janleroux/proj-roro/316941 (1).png

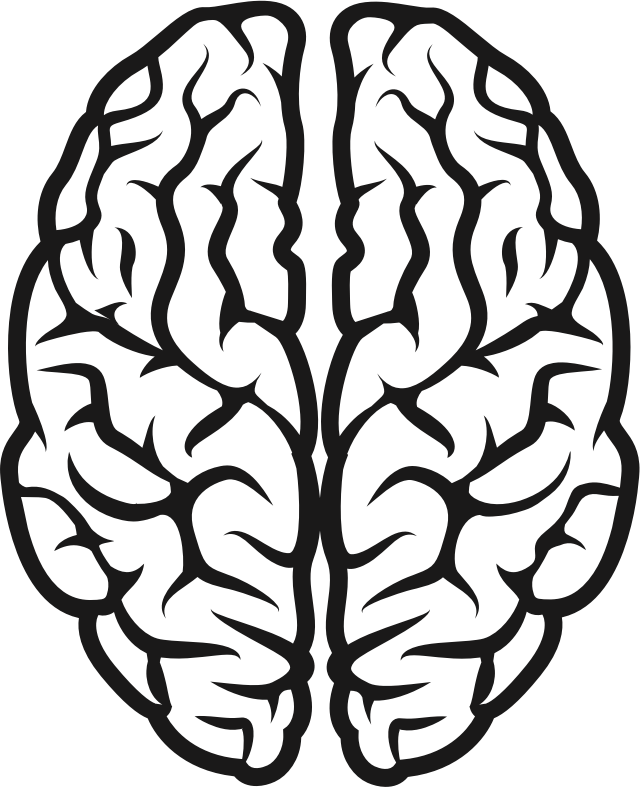
316941 (1).png
